RetroNynjah/CBM-Drive-ID-Switch/images/rev1/build.jpg

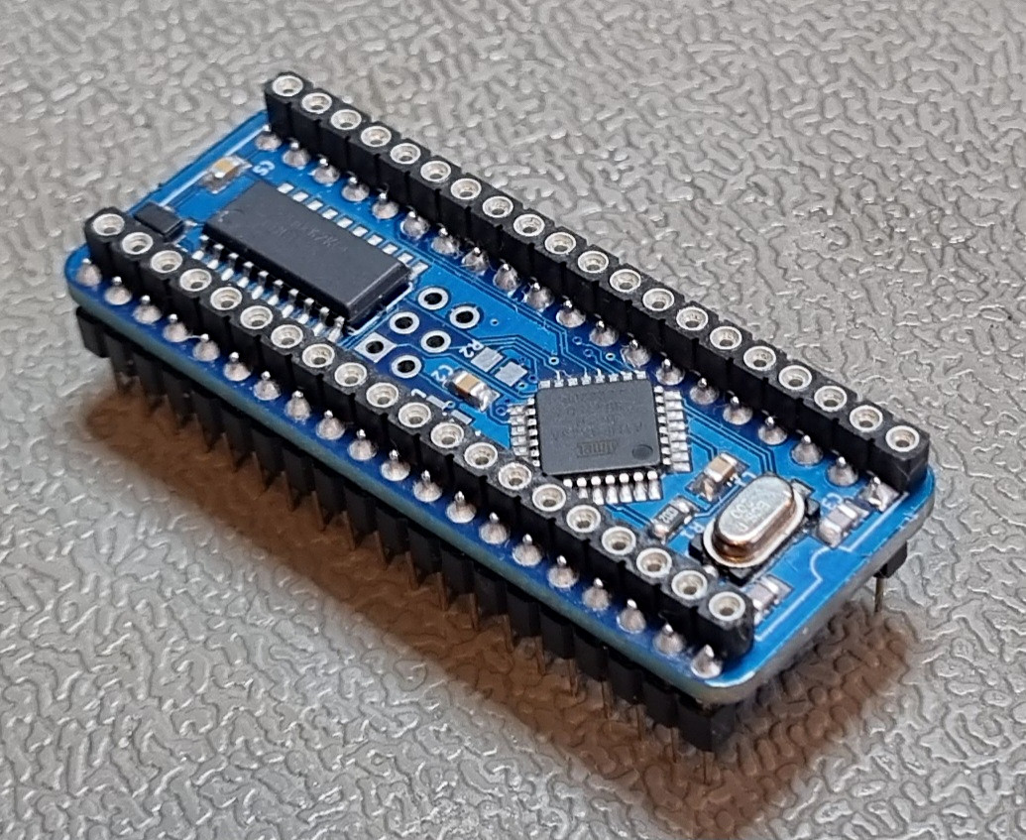
images/rev1/build.jpg
